DangerousPrototypes/Bus_Pirate/art/BP LCD v3a.tif

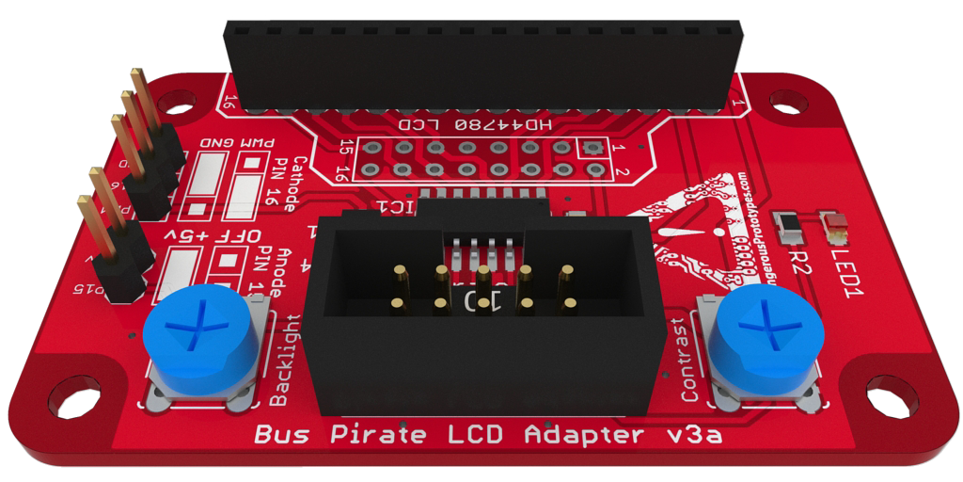
art/BP LCD v3a.tif
