DangerousPrototypes/Bus_Pirate/art/BusPirate4c-SketchupModel-rendering.jpg

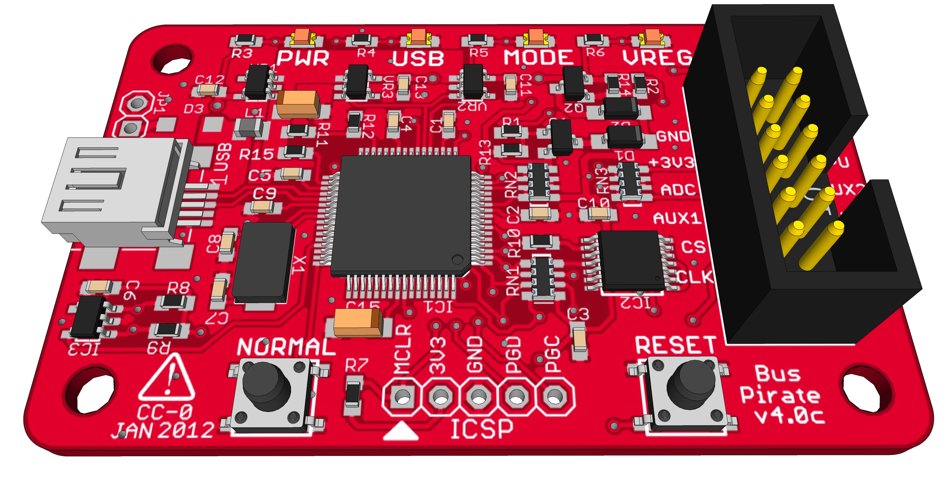
art/BusPirate4c-SketchupModel-rendering.jpg
