DangerousPrototypes/Bus_Pirate/art/BusPirateSSOP.3.5e.jpg

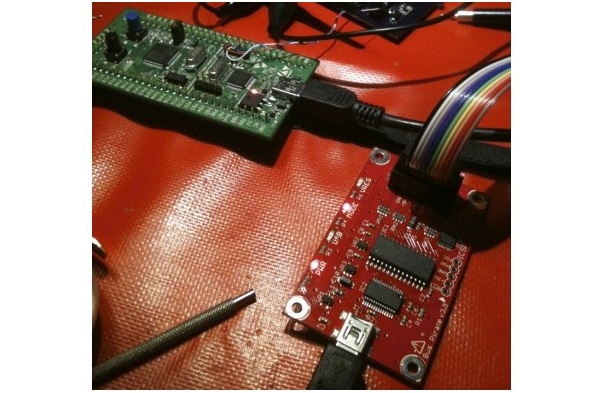
art/BusPirateSSOP.3.5e.jpg
