DangerousPrototypes/Bus_Pirate/documents/buspirate_refcard.png

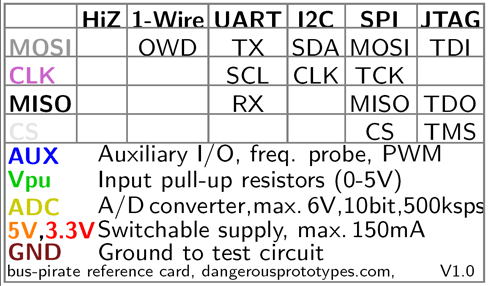
documents/buspirate_refcard.png
