DangerousPrototypes/Bus_Pirate/documents/overview450.png

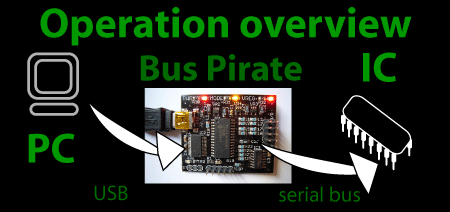
documents/overview450.png
