DangerousPrototypes/Bus_Pirate/hardware-other/BPv3-HD44780_LCD/44780-LCD-v1.jpg

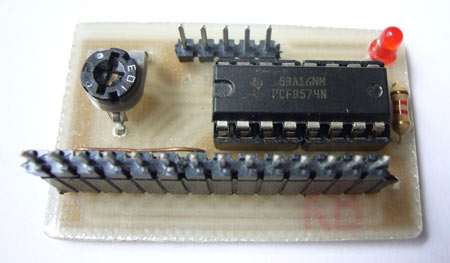
hardware-other/BPv3-HD44780_LCD/44780-LCD-v1.jpg
