DangerousPrototypes/Bus_Pirate/hardware-other/BPv3-HD44780_LCDv2/bp-lcdv2-brd.png

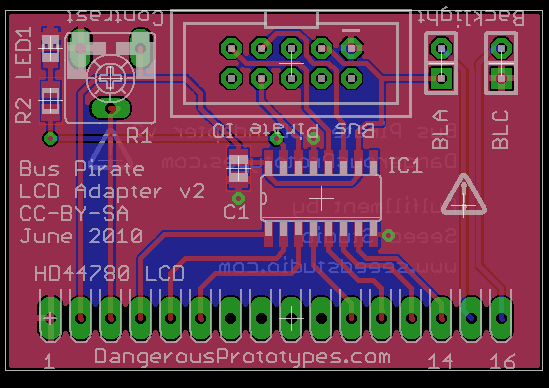
hardware-other/BPv3-HD44780_LCDv2/bp-lcdv2-brd.png
