DangerousPrototypes/Bus_Pirate/hardware-other/BPv3-HD44780_LCDv2/BP-LCDv2-CCT.png

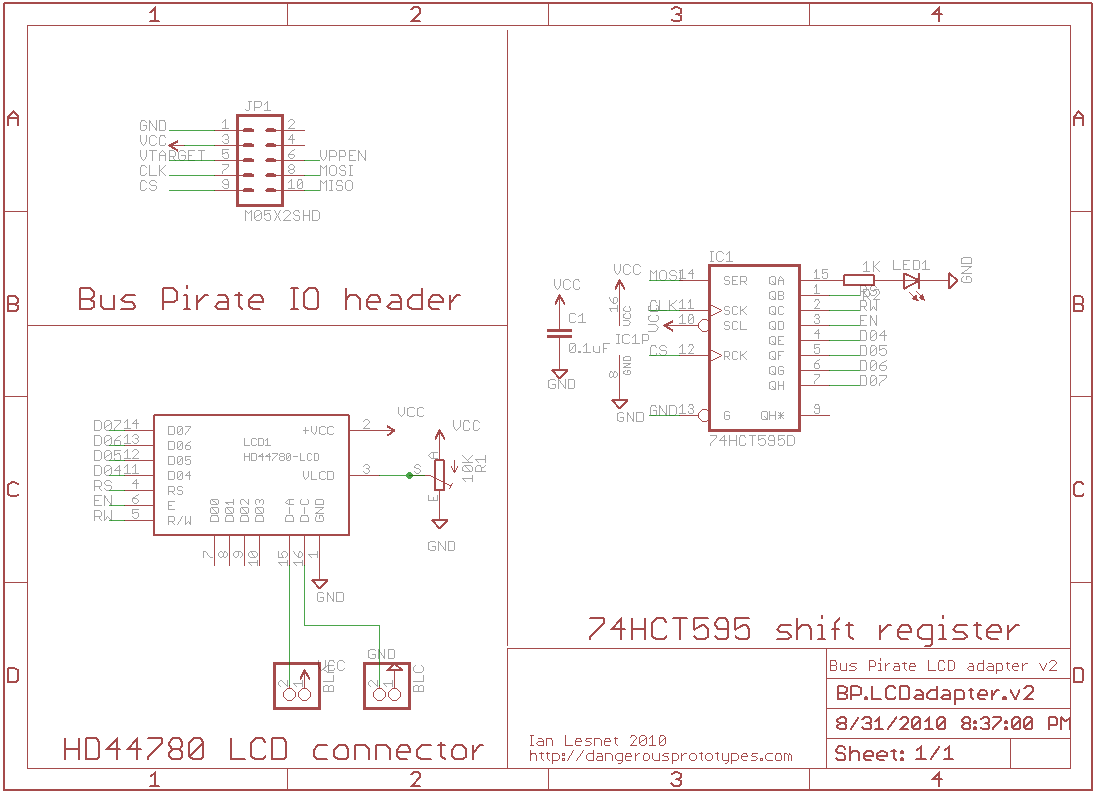
hardware-other/BPv3-HD44780_LCDv2/BP-LCDv2-CCT.png
