DangerousPrototypes/Bus_Pirate/hardware-other/BPv3-HD44780_LCDv2/BP.LCDadapter.v2b.brd.png

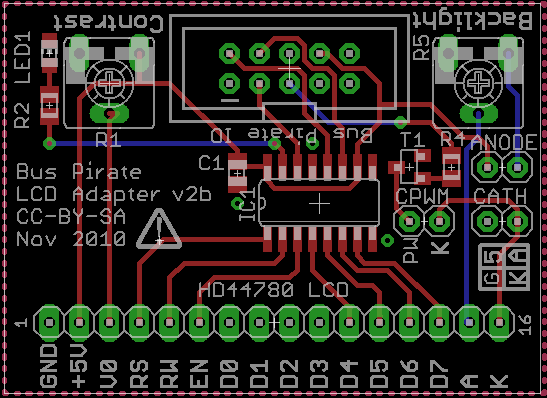
hardware-other/BPv3-HD44780_LCDv2/BP.LCDadapter.v2b.brd.png
