DangerousPrototypes/Bus_Pirate/hardware-other/BPv3-HD44780_LCDv2/male.jpg

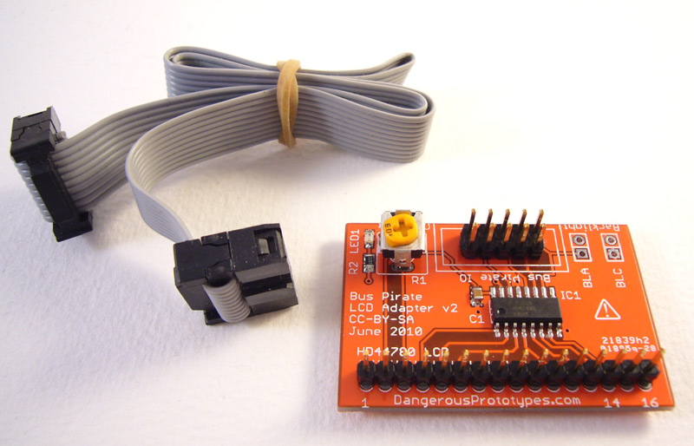
hardware-other/BPv3-HD44780_LCDv2/male.jpg
