DangerousPrototypes/Bus_Pirate/hardware-other/BPv4-HD44780_LCD/BPv4-PassiveLCDv1.sch.png

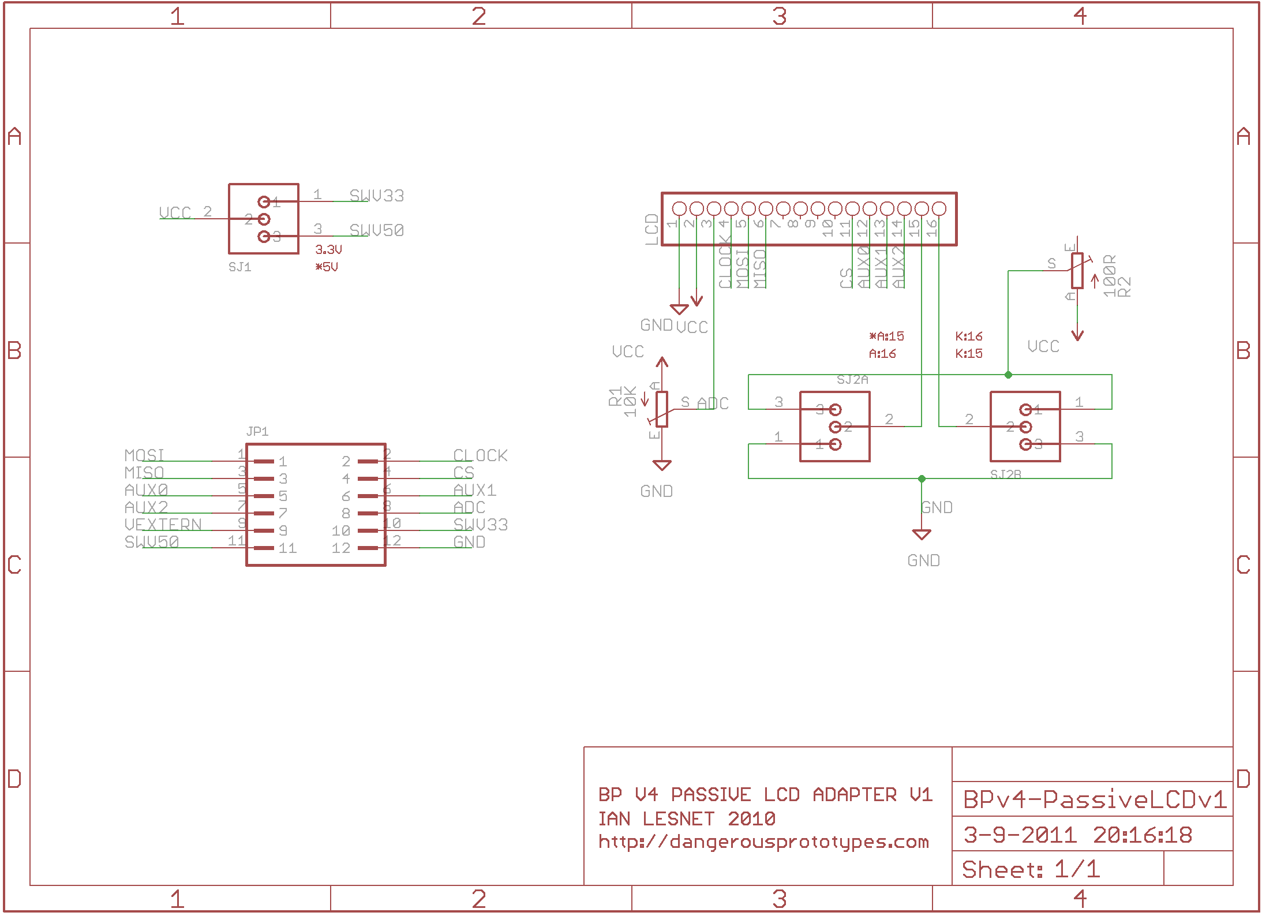
hardware-other/BPv4-HD44780_LCD/BPv4-PassiveLCDv1.sch.png
