DangerousPrototypes/Bus_Pirate/hardware-other/BPv4-HD44780_LCD/BPv4LCDadapter.v4b.sch.png

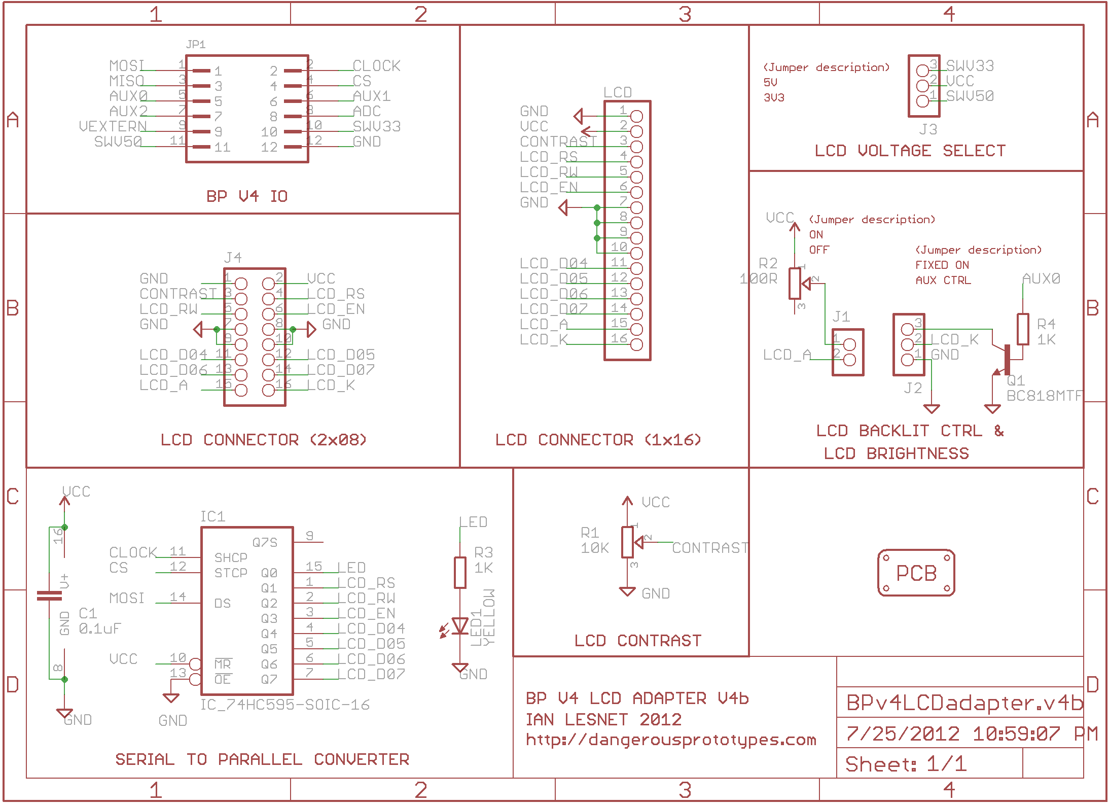
hardware-other/BPv4-HD44780_LCD/BPv4LCDadapter.v4b.sch.png
