DangerousPrototypes/Bus_Pirate/hardware-other/LIN/LIN-MCP2021-v1a.png

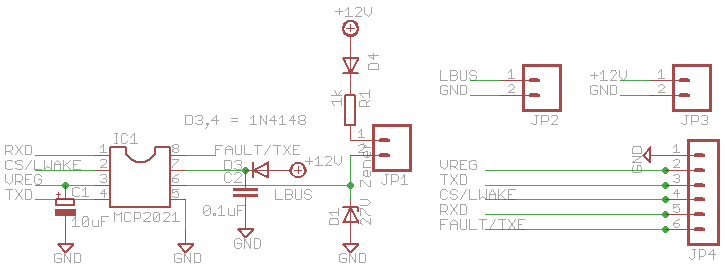
hardware-other/LIN/LIN-MCP2021-v1a.png
