DangerousPrototypes/Bus_Pirate/hardware-other/PiratePICprog/bp-hvp-back.jpg

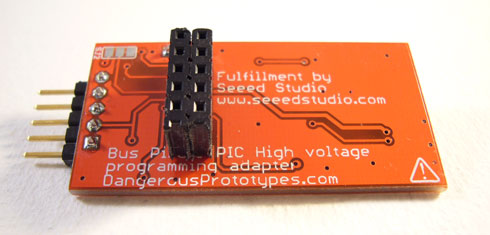
hardware-other/PiratePICprog/bp-hvp-back.jpg
