DangerousPrototypes/Bus_Pirate/hardware-other/PiratePICprog/bp-hvp-front.jpg

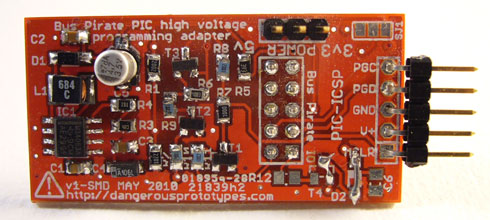
hardware-other/PiratePICprog/bp-hvp-front.jpg
