DangerousPrototypes/Bus_Pirate/hardware-other/SMPS/BusPirate-SMPS.brd.png

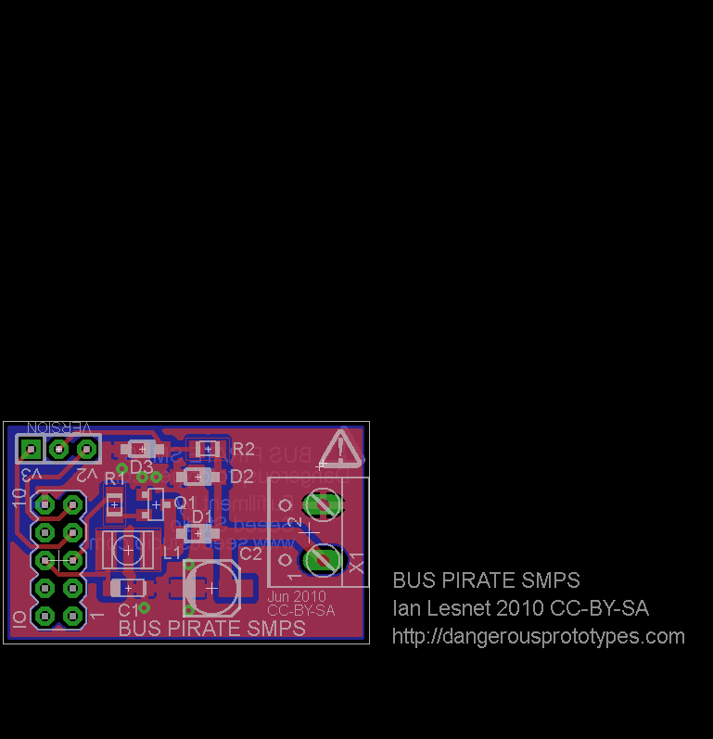
hardware-other/SMPS/BusPirate-SMPS.brd.png
