DangerousPrototypes/Bus_Pirate/hardware/v0a/brd.png

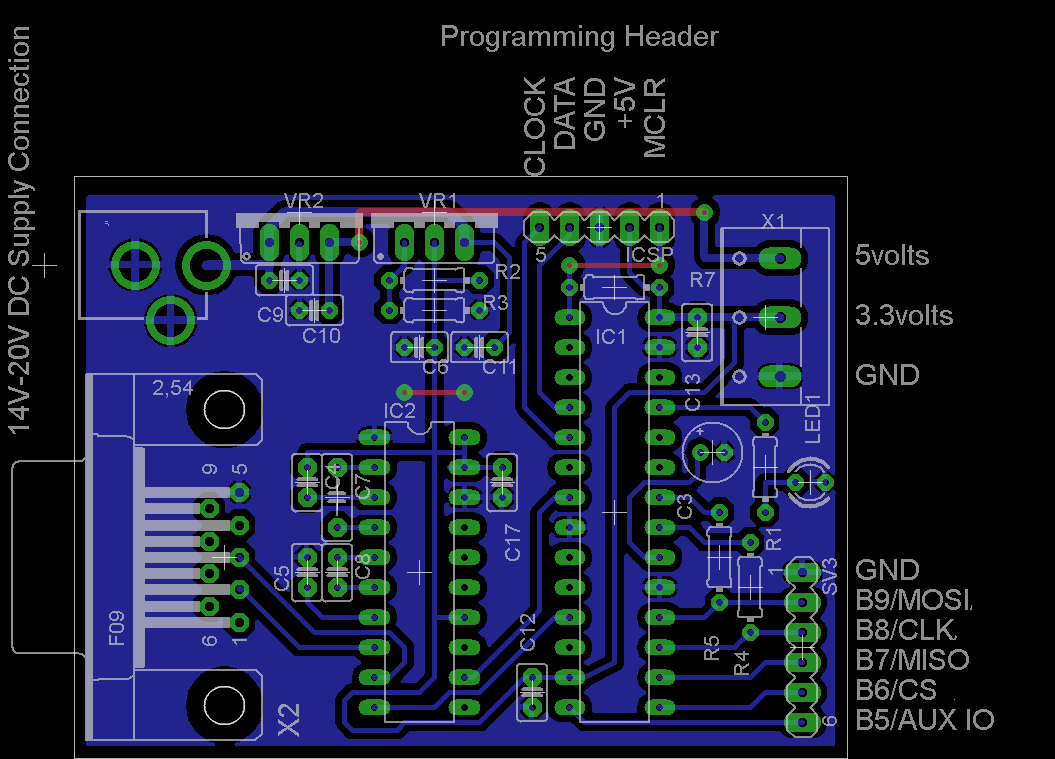
hardware/v0a/brd.png
