DangerousPrototypes/Bus_Pirate/hardware/v0a/cct.png

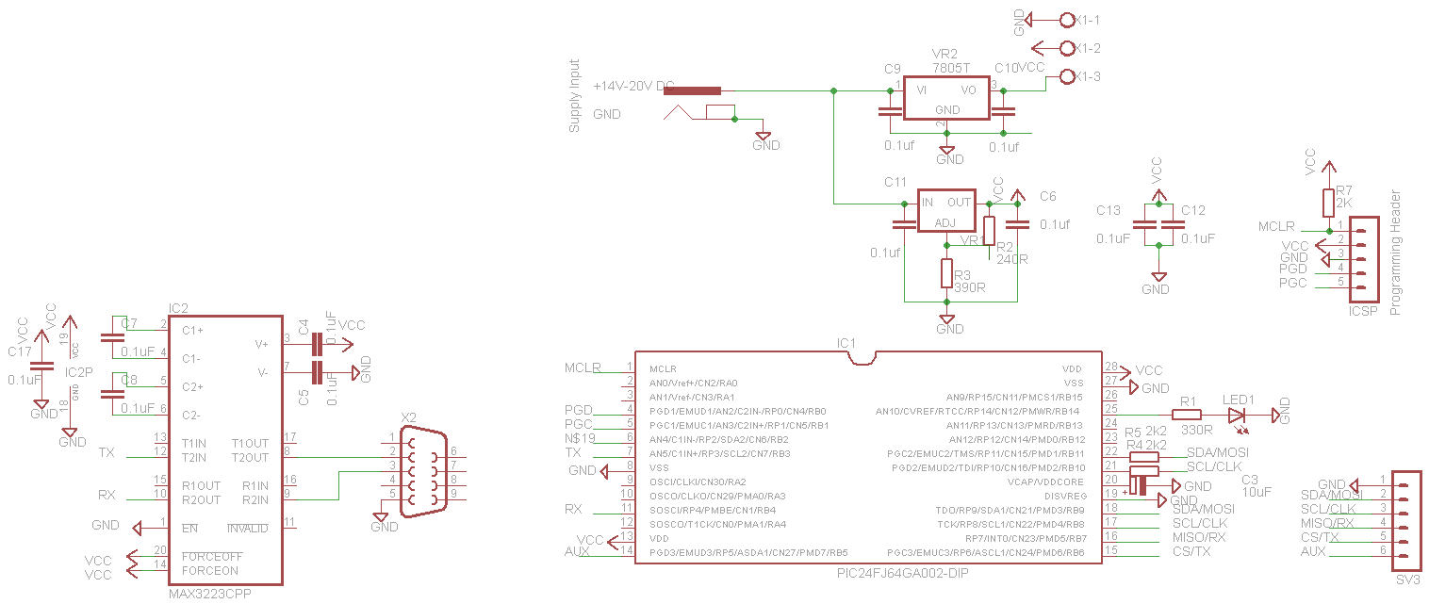
hardware/v0a/cct.png
