DangerousPrototypes/Bus_Pirate/hardware/v2a/brd.png

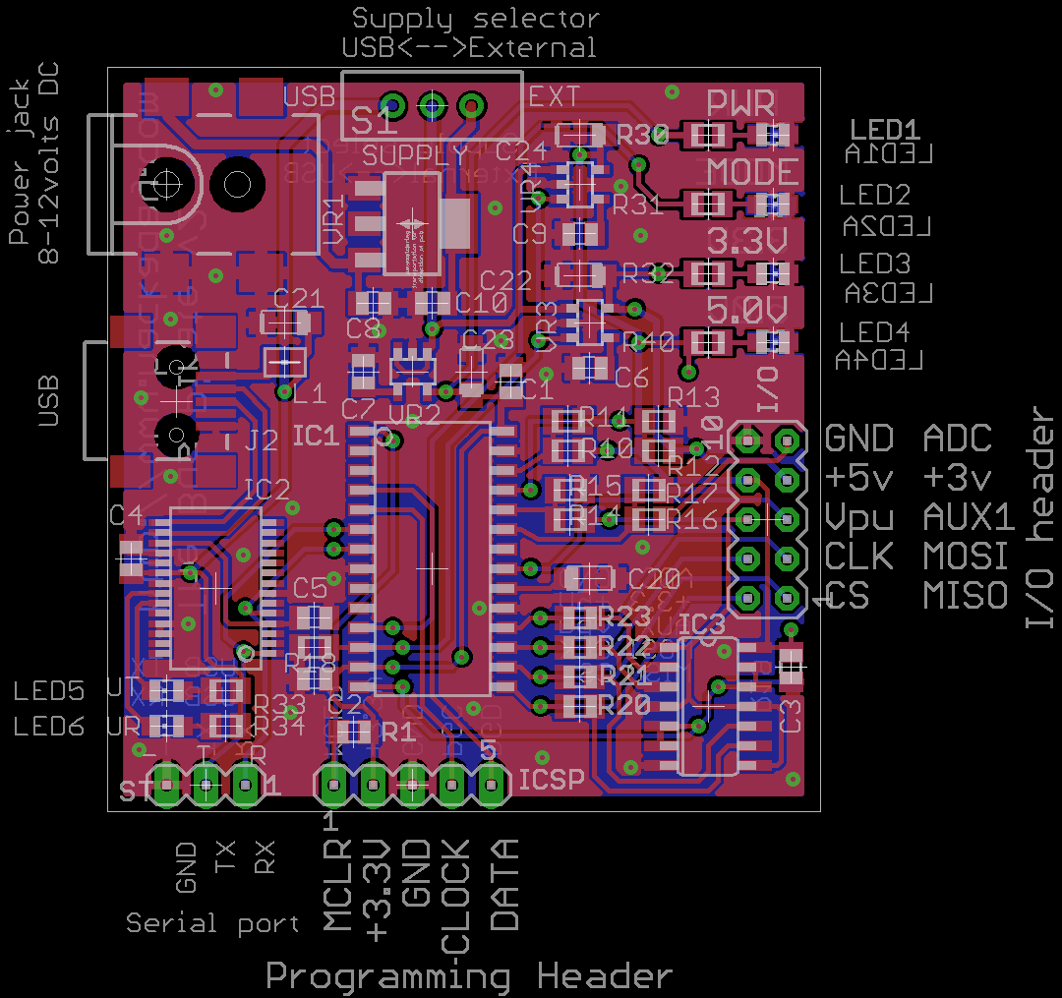
hardware/v2a/brd.png
