DangerousPrototypes/Bus_Pirate/hardware/v2go/brd.25.png

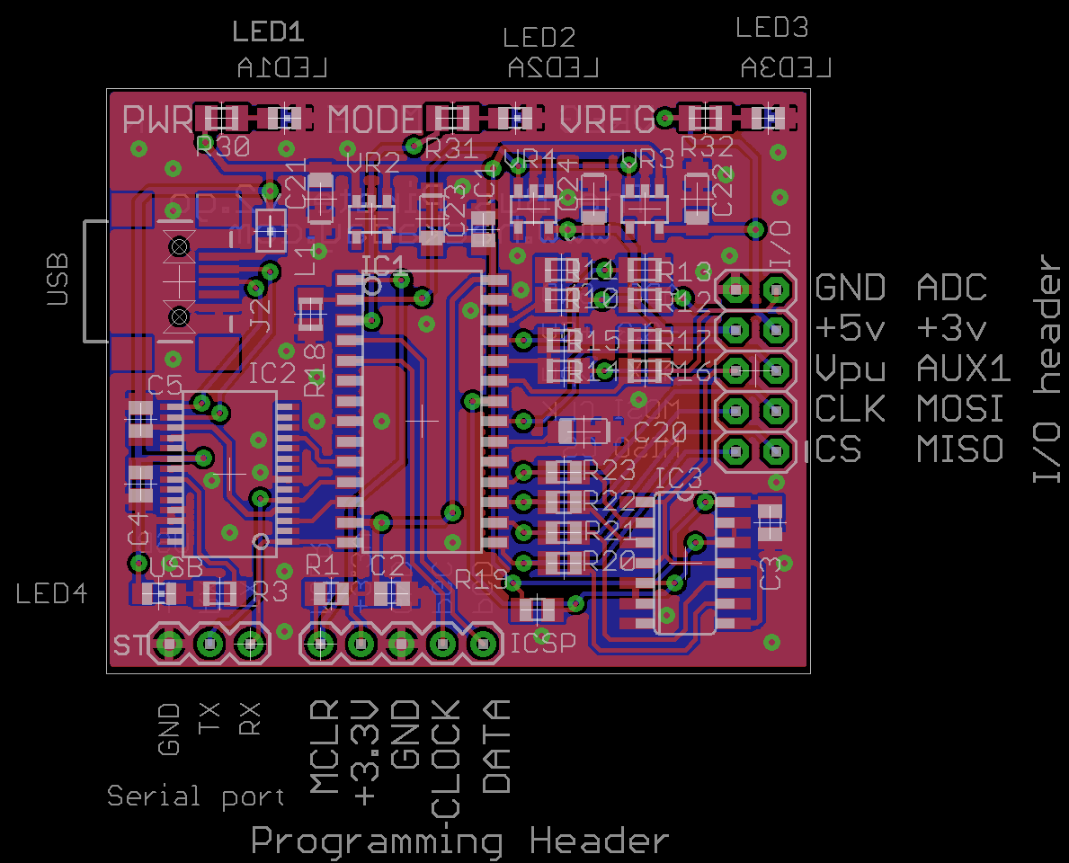
hardware/v2go/brd.25.png
