DangerousPrototypes/Bus_Pirate/hardware/v2go/BusPirate-v25.jpg

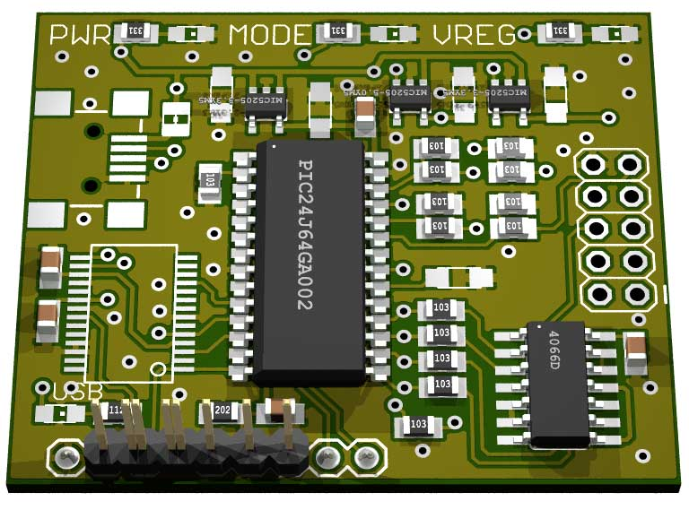
hardware/v2go/BusPirate-v25.jpg
