DangerousPrototypes/Bus_Pirate/hardware/v2go/cct25.png

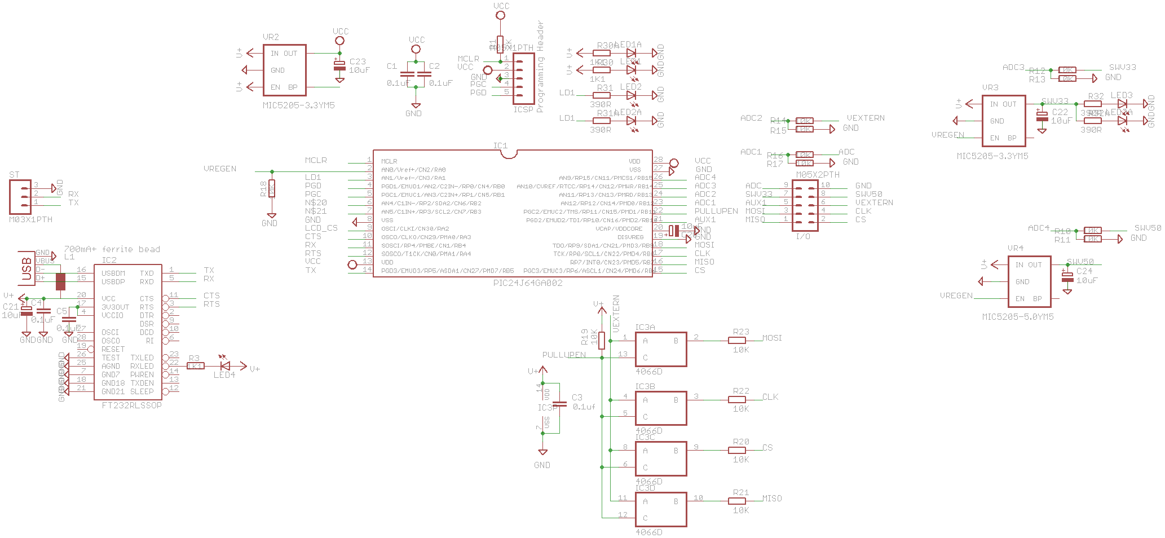
hardware/v2go/cct25.png
