DangerousPrototypes/Bus_Pirate/hardware/v5.0/tests/v5_with_China_USB/BusPirate-v5.0-SSOP.xlsx

Item | Device | Value | Package | Qty | Part no.
1 | Resistor | 1.1K | R0603 | 4 | R2, R3, R4, R6
2 | Resistor | 2K | R0603 | 1 | R1
3 | Resistor | 10K | R0603 | 2 | R5, R7
4 | Resistor | 10K 4 Resistor array | R0603 | 4 | RN1, RN2, RN3, RN4
5 | Capacitor | 0.1uF | C0603 | 6 | C1, C2, C3, C4, C5, C6
6 | Capacitor | 10uF Tantalum | SMC-A | 2 | C10, C11
7 | Capacitor | 1uF | C0603 | 3 | C7, C8, C9
8 | LED | LED Yellow | LED-0804 | 4 | LED1, LED2, LED3, LED4
9 | LED | LED Yellow (optional) | LED-0804 | 4 | LED1A, LED2A, LED3A, LED4A
10 | Ferrite | 700mA Ferrite | L0805 | 1 | L1
11 | IC | PIC24FJ64GA002 16-bit General Purpose Flash Microcontroller | SSOP-28 | 1 | IC1
12 | IC | 4066 Quad bilateral switch | TSSOP-14 | 1 | IC2
13 | IC | FT230X Basic USB to UART | SSOP-16 | 1 | IC4
14 | IC | BL1551 Analog switch | SOT-363 | 2 | IC5, IC6
15 | IC | 3.3V MCP1801T-3302I/OT 150ma Low-Noise LDO | SOT-23-5 | 2 | VR1, VR2
16 | IC | 5.0V MCP1801T-5002I/OT 150ma Low-Noise LDO | SOT-23-5 | 1 | VR3
17 | Connector | USB micro-B female | USB micro-b | 1 | CON3
18 | Connector | 0.1" shoruded right angled male header Molex 70553-0044 | 1x10 | 1 | CON1
19 | Connector | 0.1" male header | 1x06 | 1 | CON2
